fehlfarbe/ESP32-Alarm-clock/doc/photo01.jpg

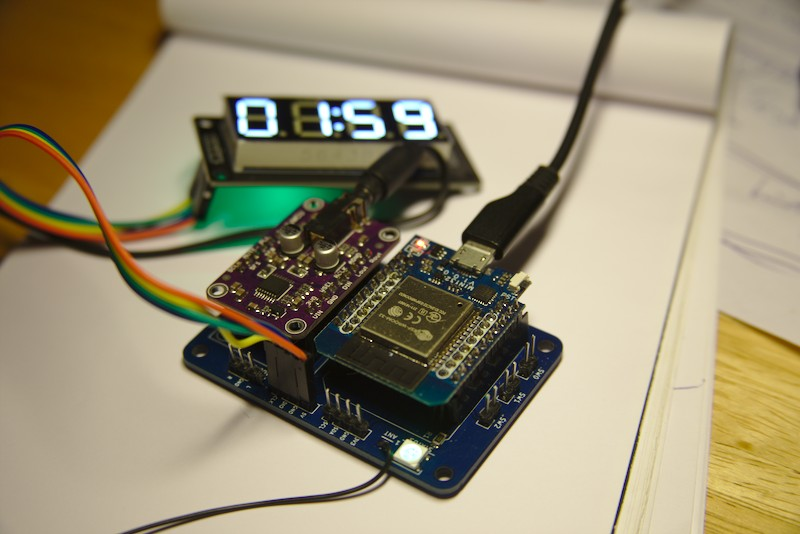
doc/photo01.jpg
