fehlfarbe/ESP32-Alarm-clock/doc/photo02.jpg

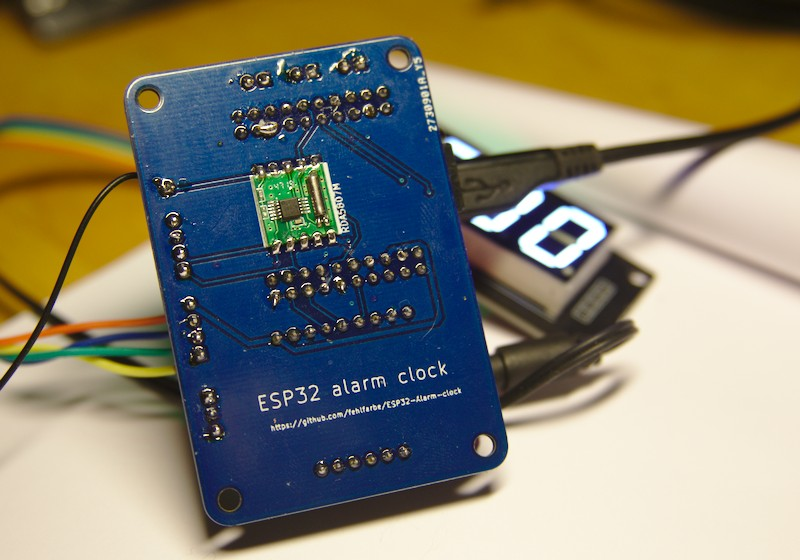
doc/photo02.jpg
